PTBresearch/Air-Quality-Measurement-Example/Dokumentation/Arduino/2023-11-20_Breadboard_V1_Front.jpg

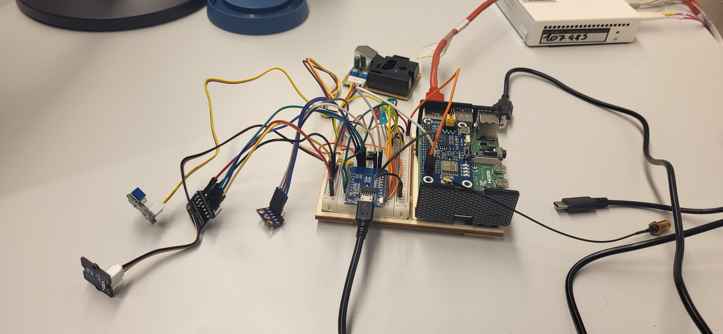
Dokumentation/Arduino/2023-11-20_Breadboard_V1_Front.jpg
