PTBresearch/Air-Quality-Measurement-Example/Dokumentation/Arduino/2024-03-13_Breadboard_V2_Top_2.jpg

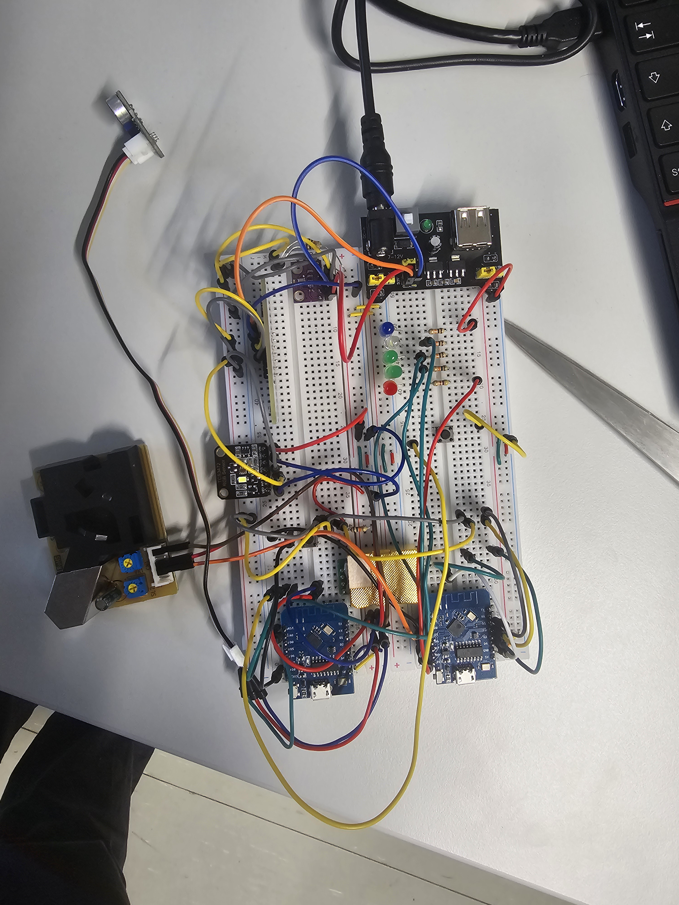
Dokumentation/Arduino/2024-03-13_Breadboard_V2_Top_2.jpg
