PTBresearch/Air-Quality-Measurement-Example/Dokumentation/Arduino/2024-05-07_AQM-V2_Side.jpg

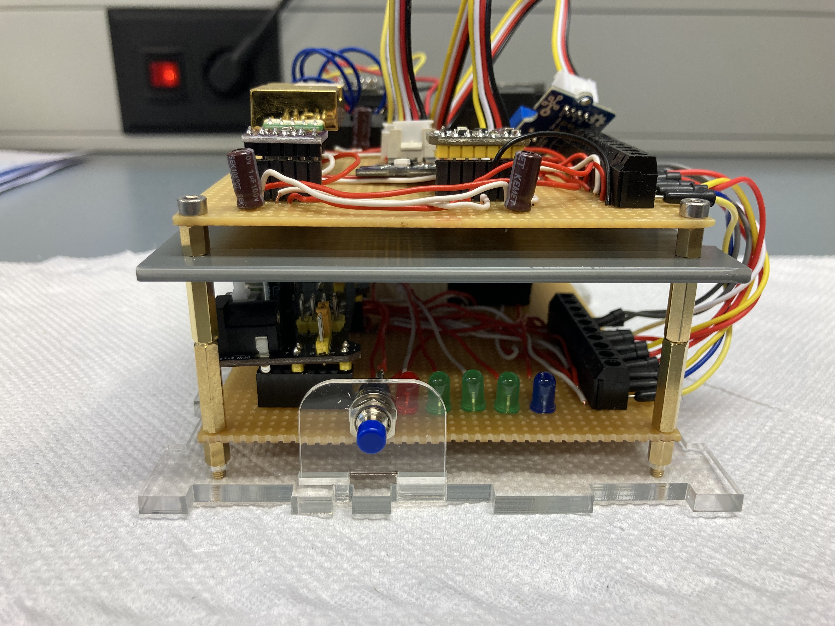
Dokumentation/Arduino/2024-05-07_AQM-V2_Side.jpg
