PTBresearch/Air-Quality-Measurement-Example/Dokumentation/Arduino/2024-05-15_Breadboard_V2.jpg

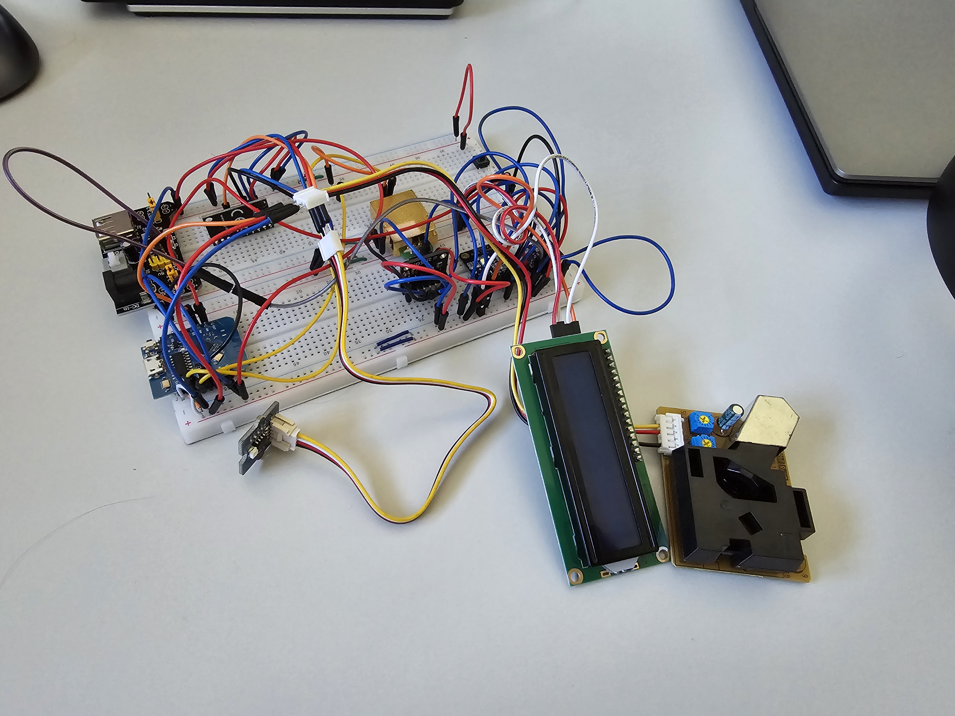
Dokumentation/Arduino/2024-05-15_Breadboard_V2.jpg
