PTBresearch/Air-Quality-Measurement-Example/Dokumentation/Arduino/2024-05-15_Breadboard_V2_Top.jpg

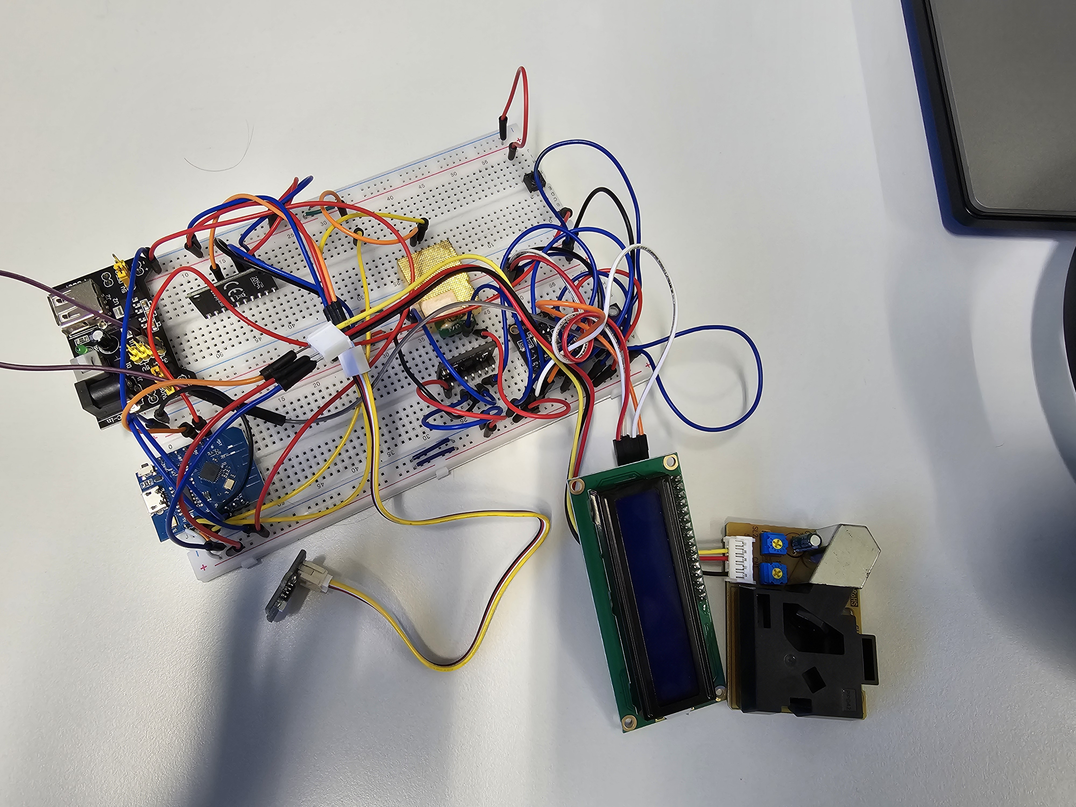
Dokumentation/Arduino/2024-05-15_Breadboard_V2_Top.jpg
