PTBresearch/Air-Quality-Measurement-Example/Dokumentation/Arduino/2025-09-16-PCB-V3-Blender-Render-PCB.png

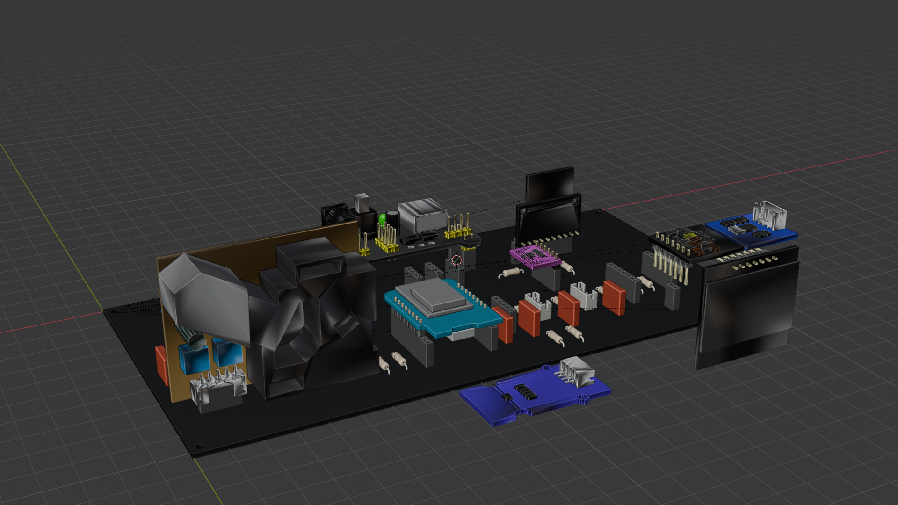
Dokumentation/Arduino/2025-09-16-PCB-V3-Blender-Render-PCB.png
