PTBresearch/Air-Quality-Measurement-Example/Dokumentation/Arduino/Arduino.drawio.png

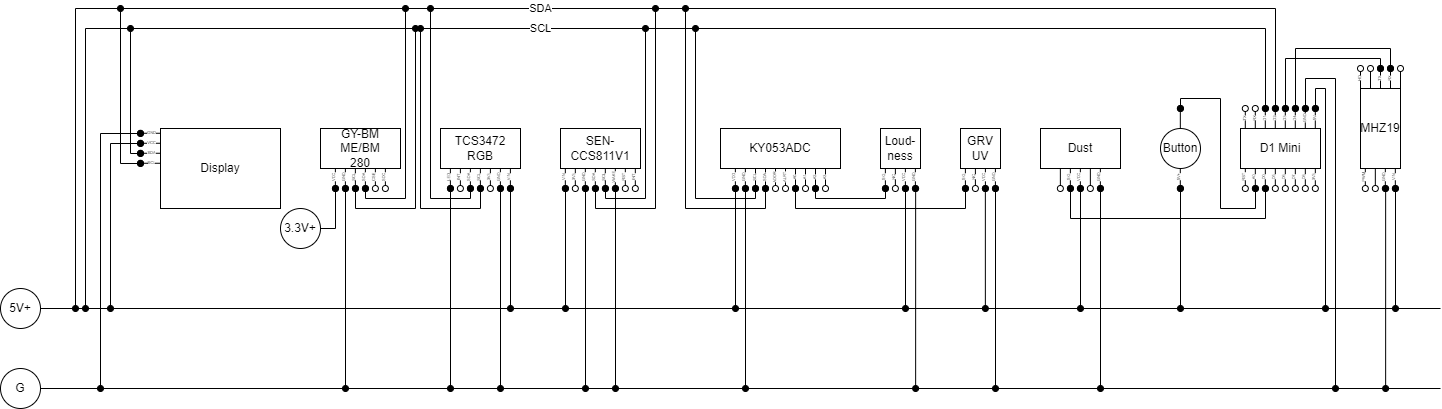
Dokumentation/Arduino/Arduino.drawio.png
