PTBresearch/Air-Quality-Measurement-Example/Arduino-Code/Main/typk.ino

void typk_INIT() {
  Serial.println("Typk Beginn");

  Serial.print("Initializing sensor...");
  if (! mcp.begin(0x60)) {
    Serial.println("Sensor not found. Check wiring!");
    while (1);
  }

  Serial.println("Found MCP9600!");

  /* Set and print ambient resolution */
  mcp.setAmbientResolution(ambientRes);
  Serial.print("Ambient Resolution set to: ");
  switch (ambientRes) {
    case RES_ZERO_POINT_25:    Serial.println("0.25°C"); break;
    case RES_ZERO_POINT_125:   Serial.println("0.125°C"); break;
    case RES_ZERO_POINT_0625:  Serial.println("0.0625°C"); break;
    case RES_ZERO_POINT_03125: Serial.println("0.03125°C"); break;
  }

  mcp.setADCresolution(MCP9600_ADCRESOLUTION_18);
  Serial.print("ADC resolution set to ");
  switch (mcp.getADCresolution()) {
    case MCP9600_ADCRESOLUTION_18:   Serial.print("18"); break;
    case MCP9600_ADCRESOLUTION_16:   Serial.print("16"); break;
    case MCP9600_ADCRESOLUTION_14:   Serial.print("14"); break;
    case MCP9600_ADCRESOLUTION_12:   Serial.print("12"); break;
  }
  Serial.println(" bits");

  mcp.setThermocoupleType(MCP9600_TYPE_K);
  Serial.print("Thermocouple type set to ");
  switch (mcp.getThermocoupleType()) {
    case MCP9600_TYPE_K:  Serial.print("K"); break;
    case MCP9600_TYPE_J:  Serial.print("J"); break;
    case MCP9600_TYPE_T:  Serial.print("T"); break;
    case MCP9600_TYPE_N:  Serial.print("N"); break;
    case MCP9600_TYPE_S:  Serial.print("S"); break;
    case MCP9600_TYPE_E:  Serial.print("E"); break;
    case MCP9600_TYPE_B:  Serial.print("B"); break;
    case MCP9600_TYPE_R:  Serial.print("R"); break;
  }
  Serial.println(" type");

  mcp.setFilterCoefficient(3);
  Serial.print("Filter coefficient value set to: ");
  Serial.println(mcp.getFilterCoefficient());

  mcp.setAlertTemperature(1, 30);
  Serial.print("Alert #1 temperature set to ");
  Serial.println(mcp.getAlertTemperature(1));
  mcp.configureAlert(1, true, true);  // alert 1 enabled, rising temp

  mcp.enable(true);

  Serial.println("Typk Ready");
}

void typk_DATA() {

  sensors_typk1_temp_hot["value"] = mcp.readThermocouple();
  sensors_typk1_temp_cold["value"] = mcp.readAmbient();
  sensors_typk1_adc["value"] = mcp.readADC() * 2;

}
