PTBresearch/Air-Quality-Measurement-Example/Dokumentation/Arduino/2024-03-27_Circut_Board_Idea_Connectors.jpg

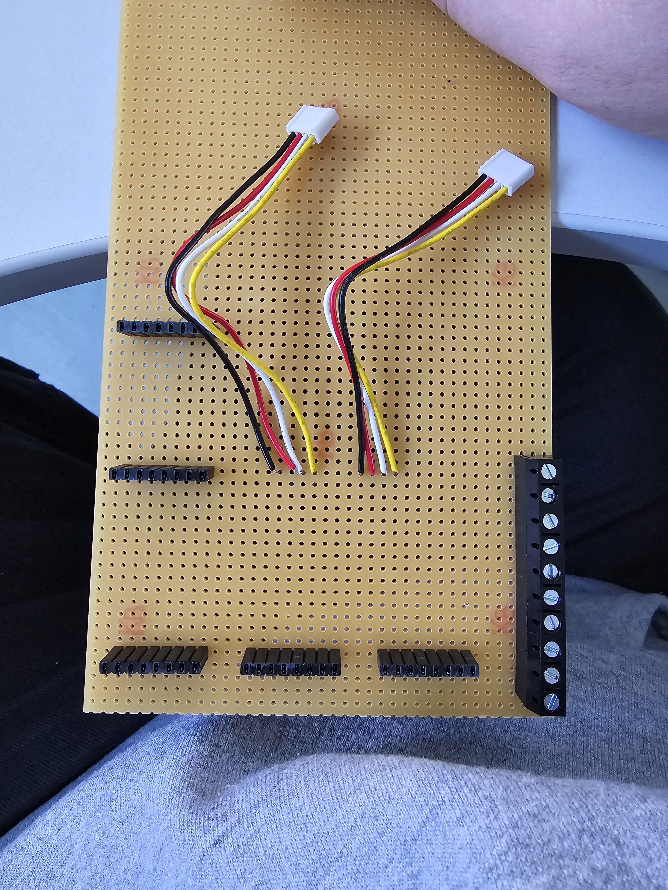
Dokumentation/Arduino/2024-03-27_Circut_Board_Idea_Connectors.jpg
