PTBresearch/Air-Quality-Measurement-Example/Dokumentation/Arduino/2024-04-11_Full_Circut_Board_Idea.jpg

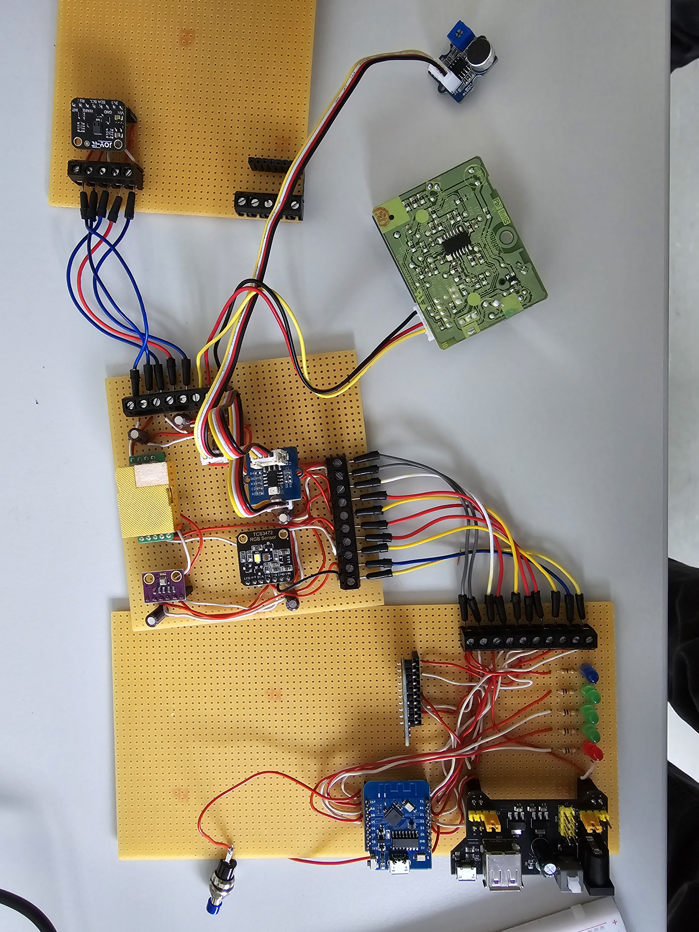
Dokumentation/Arduino/2024-04-11_Full_Circut_Board_Idea.jpg
